Sierra-Lobo/imu-stamp/design/iam-20380-orientation.PNG

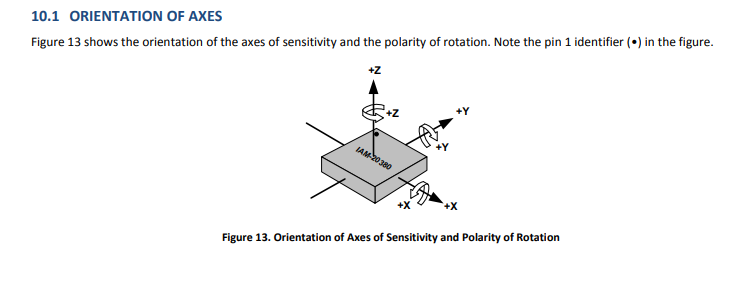
design/iam-20380-orientation.PNG
