Sierra-Lobo/imu-stamp/design/iam-20380-ref-ckt.PNG

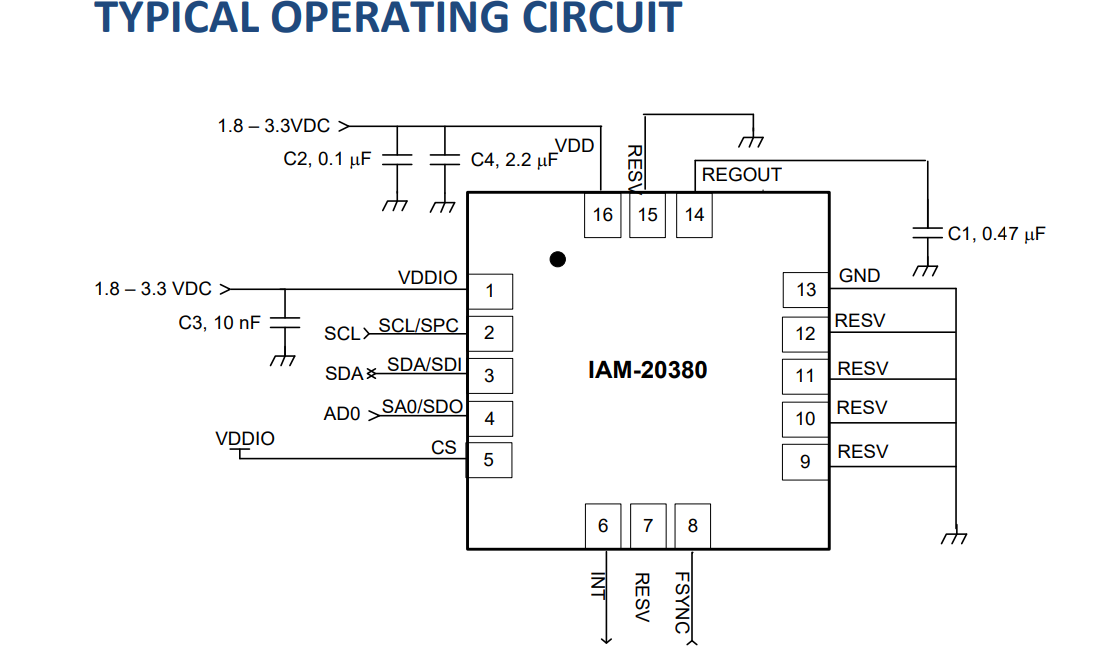
design/iam-20380-ref-ckt.PNG
