Sierra-Lobo/imu-stamp/design/mc3419-orientation.PNG

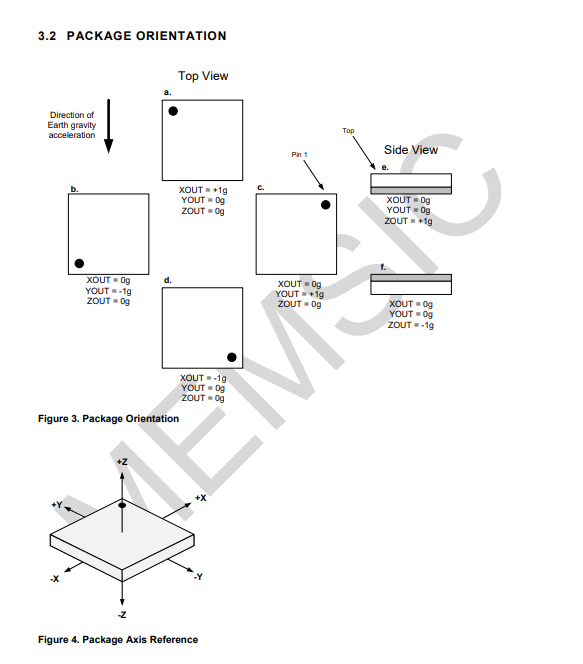
design/mc3419-orientation.PNG
