Sierra-Lobo/imu-stamp/design/MMC5603-ref-ckt.PNG

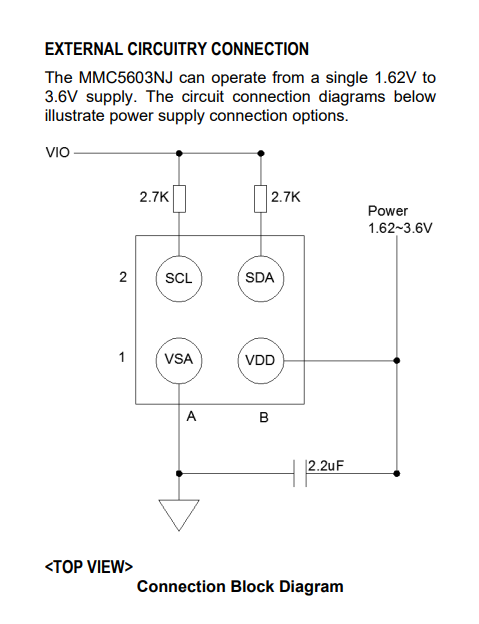
design/MMC5603-ref-ckt.PNG
